MustSeeMelons/can_esp32/main/tasks_common.h

#ifndef TASKS_COMMON_H_
#define TASKS_COMMON_H_

#define OBD_READ_TASK_STACK_SIZE 2048
#define OBD_READ_TASK_PRIORITY   5
#define OBD_READ_TASK_CORE_ID    1

#define OBD_WRITE_TASK_STACK_SIZE 2048
#define OBD_WRITE_TASK_PRIORITY   5
#define OBD_WRITE_TASK_CORE_ID    1

#define HTTP_SERVER_TASK_STACK_SIZE 4096
#define HTTP_SERVER_TASK_PRIORITY   4
#define HTTP_SERVER_TASK_CORE_ID    0

#define SD_TASK_STACK_SIZE 8192
#define SD_TASK_PRIORITY   8
#define SD_TASK_CODE_ID    0

#define I2S_TASK_STACK_SIZE 4096
#define I2S_TASK_PRIORITY   9
#define I2S_TASK_CODE_ID    1

#endif
